Adrian-tech-bot/HotWheels/Hot_Wheels_Electronics/Hot_Wheels_Electronics.kicad_sch

## KiCad design Hot_Wheels_Electronics/Hot_Wheels_Electronics.kicad_sch (2026-09-03, an earlier design)

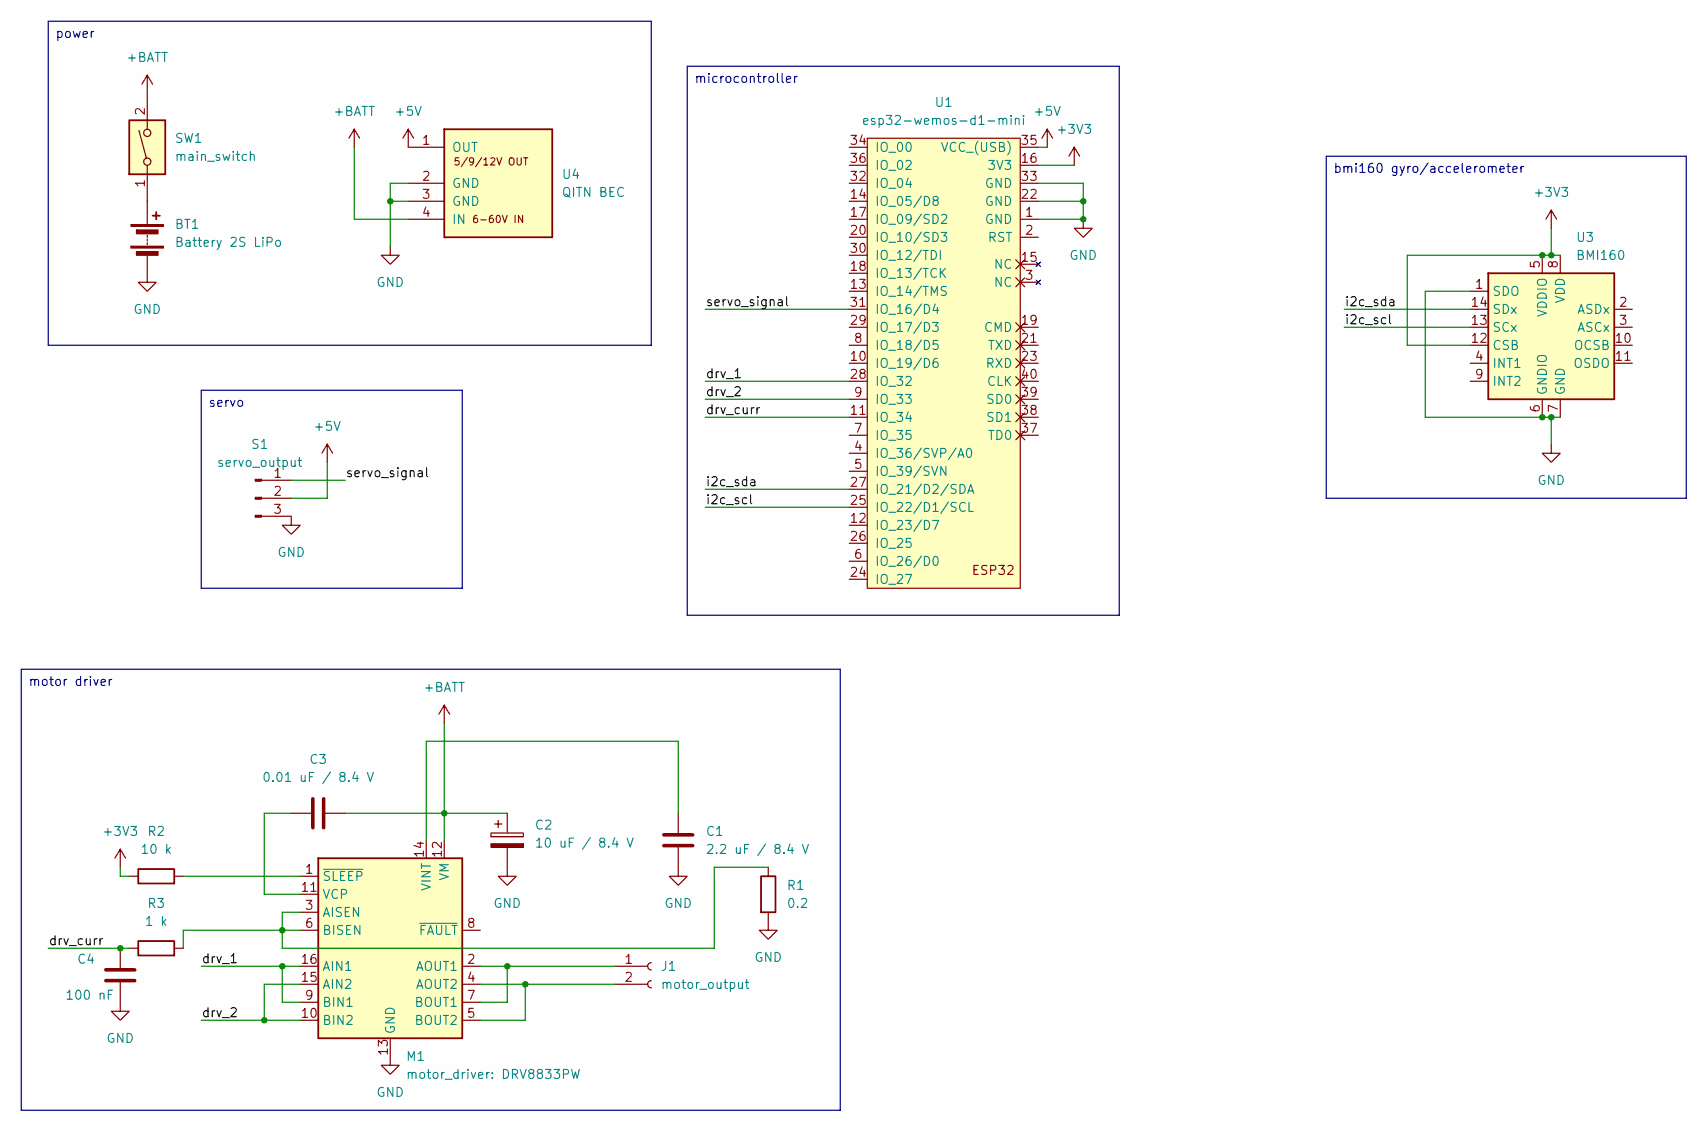
[picture p2: schematic Hot_Wheels_Electronics.kicad_sch]

Parts:
BT1: Battery 2S LiPo; JST_PH_S2B-PH-SM4-TB_1x02-1MP_P2.00mm_Horizontal
C1: 2.2 uF / 8.4 V; C_1206_3216Metric_Pad1.33x1.80mm_HandSolder
C2: 10 uF / 8.4 V
C3: 0.01 uF / 8.4 V; C_1206_3216Metric_Pad1.33x1.80mm_HandSolder
C4: 100 nF
J1: motor_output; JST_PH_S2B-PH-K_1x02_P2.00mm_Horizontal
M1: motor_driver: DRV8833PW; TSSOP-16_4.4x5mm_P0.65mm
R1: 0.2
R2: 10 k
R3: 1 k
S1: servo_output; PinHeader_1x03_P2.54mm_Vertical_SMD_Pin1Left
SW1: main_switch
U1: esp32-wemos-d1-mini; ESP32_Wemos_D1_Mini_SMD_Socket_2x20_2.54mm
U3: BMI160; Bosch_LGA-14_3x2.5mm_P0.5mm
U4: QITN BEC; BEC_QITN_Matek_Micro_18x16mm_Castellated

Connections:
+3V3: R2.1, U1.16 (3V3), U3.5 (VDDIO), U3.8 (VDD), U3.12 (CSB)
+5V: S1.2, U1.35 (VCC_(USB)), U4.1 (OUT)
+BATT: C2.1, C3.2, M1.12 (VM), SW1.2, U4.4 (IN)
GND: BT1.2 (-), C1.2, C2.2, C4.2, M1.13 (GND), R1.2, S1.3, U1.1 (GND), U1.22 (GND), U1.33 (GND), U3.1 (SDO), U3.6 (GNDIO), U3.7 (GND), U4.2 (GND), U4.3 (GND)
unnamed: BT1.1 (+), SW1.1
unnamed: C1.1, M1.14 (VINT)
unnamed: C3.1, M1.11 (VCP)
unnamed: J1.1, M1.2 (AOUT1), M1.7 (BOUT1)
unnamed: J1.2, M1.4 (AOUT2), M1.5 (BOUT2)
unnamed: M1.1 (~SLEEP), R2.2
unnamed: M1.3 (AISEN), M1.6 (BISEN), R1.1, R3.2
drv_1: M1.9 (BIN1), M1.16 (AIN1), U1.28 (IO_32)
drv_2: M1.10 (BIN2), M1.15 (AIN2), U1.9 (IO_33)
drv_curr: C4.1, R3.1, U1.11 (IO_34)
i2c_scl: U1.25 (IO_22/D1/SCL), U3.13 (SCx)
i2c_sda: U1.27 (IO_21/D2/SDA), U3.14 (SDx)
servo_signal: S1.1, U1.31 (IO_16/D4)

Notes on the sheet:
servo
microcontroller
motor driver
power
bmi160 gyro/accelerometer
